mercedes-benz/ardep/_images/heartbeat_led_pcb.png

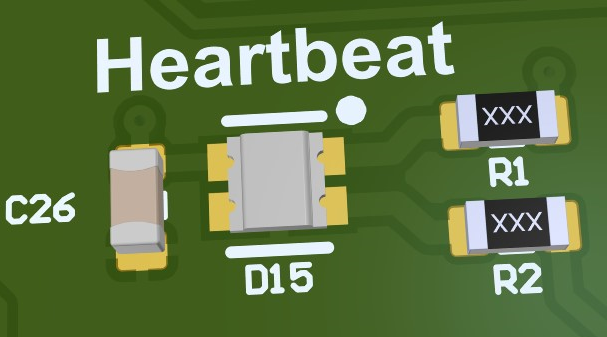
_images/heartbeat_led_pcb.png
