mercedes-benz/ardep/_images/3d_view.png

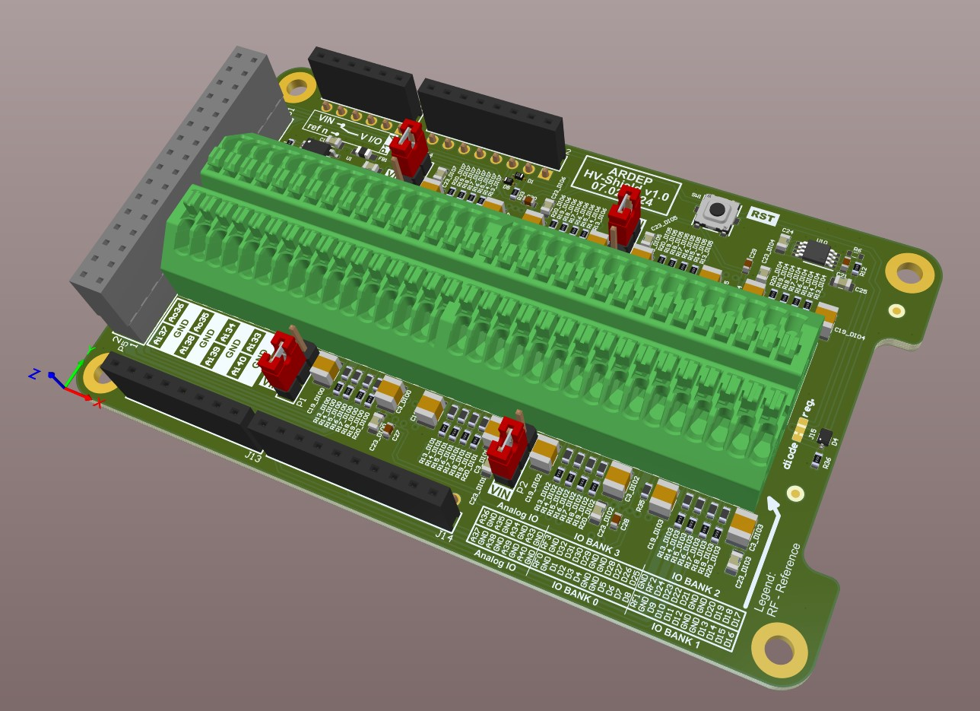
_images/3d_view.png
