mercedes-benz/ardep/_images/3d_view_v1_0_0.png

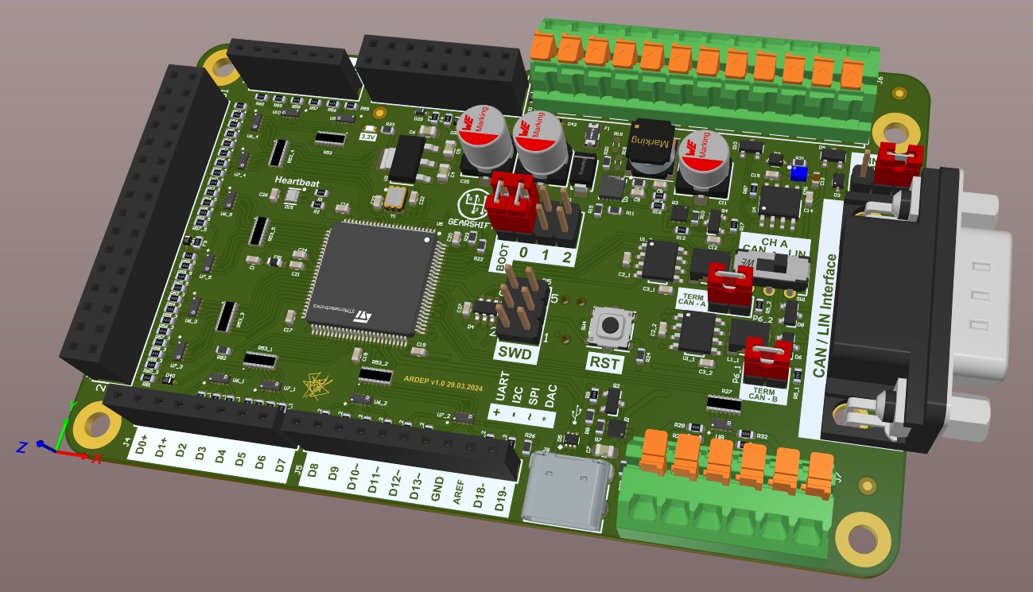
_images/3d_view_v1_0_0.png
