mercedes-benz/ardep/_images/32pin_header_rev0_1.png

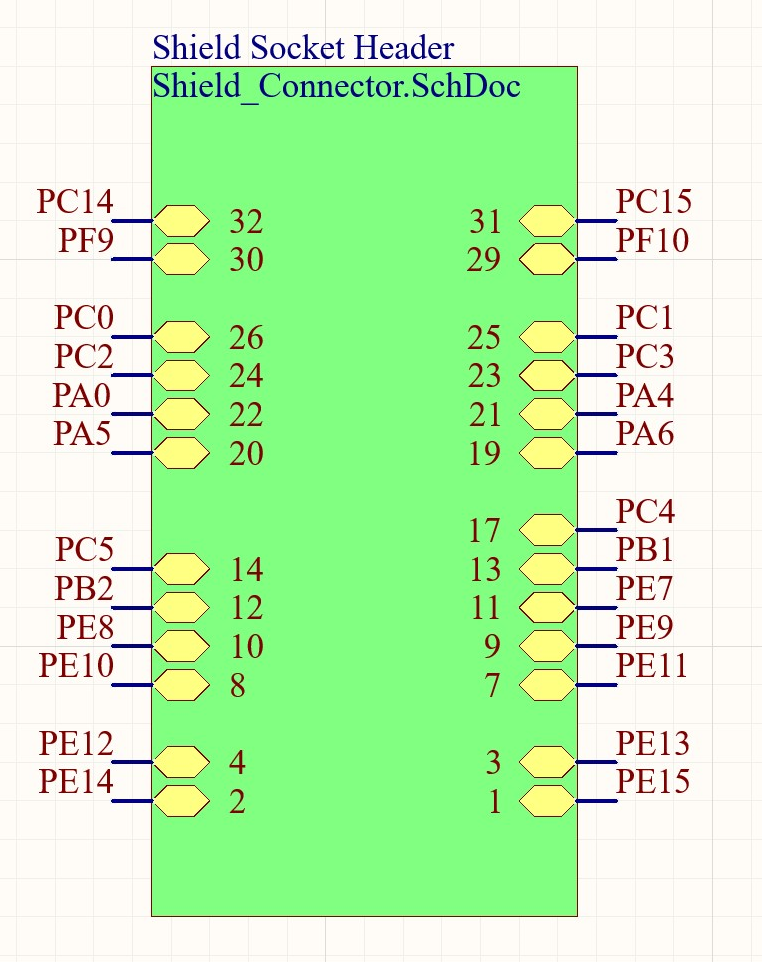
_images/32pin_header_rev0_1.png
