mercedes-benz/ardep/_images/32pin_header_rev0_2.png

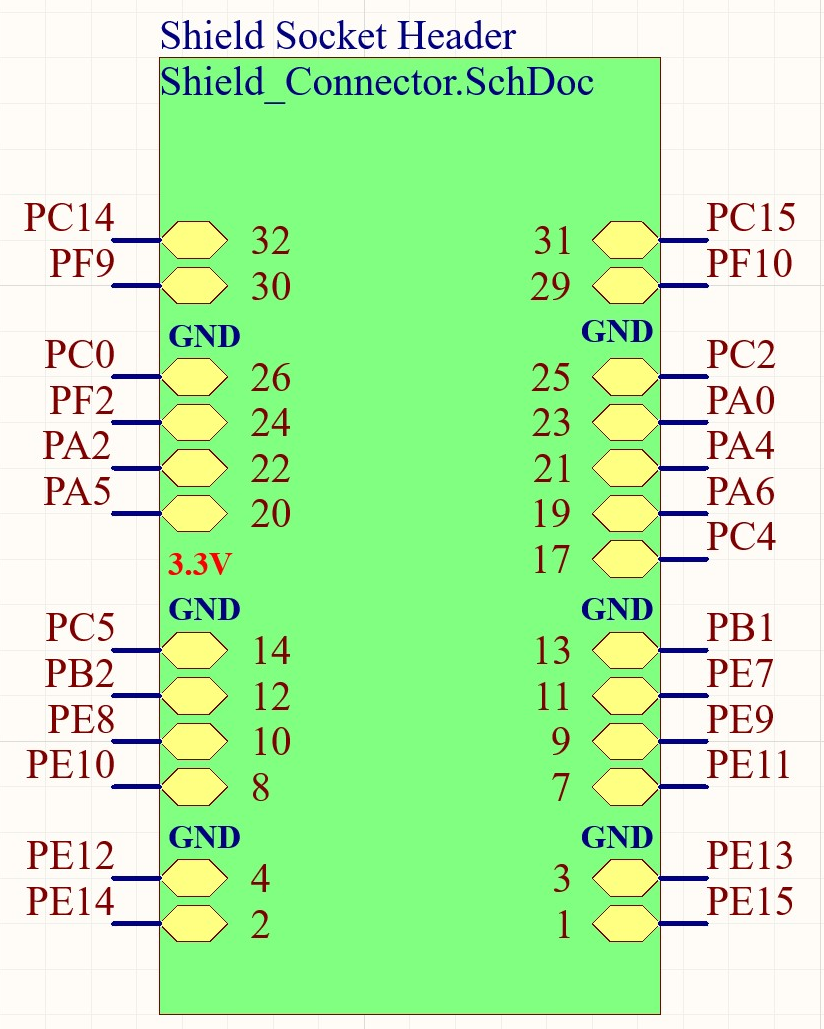
_images/32pin_header_rev0_2.png
