mercedes-benz/ardep/_images/74hc595_implementation.png

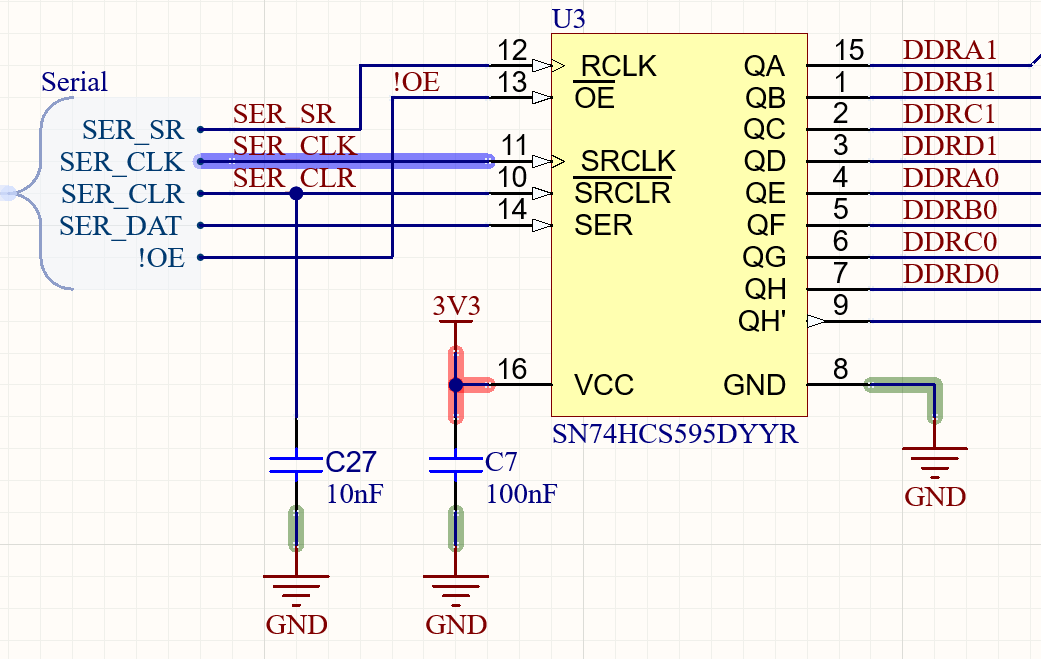
_images/74hc595_implementation.png
