mercedes-benz/ardep/_images/active_input_circuit.png

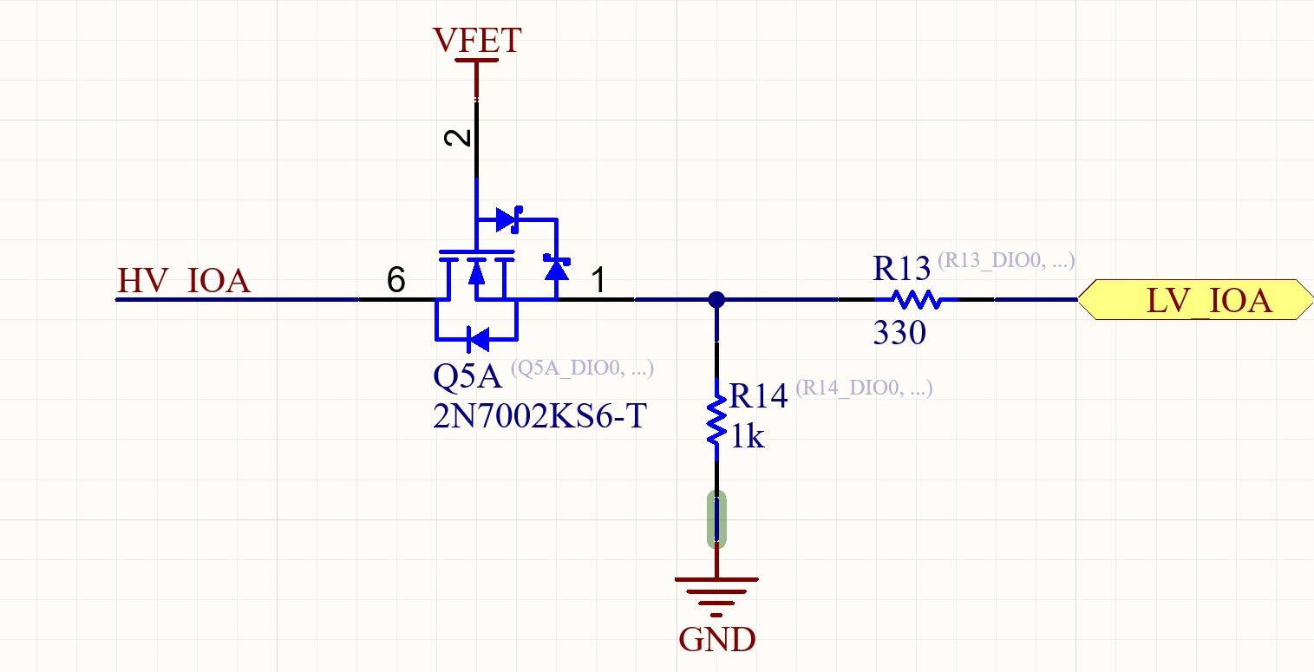
_images/active_input_circuit.png
