mercedes-benz/ardep/_images/analog_gain_amplifier.png

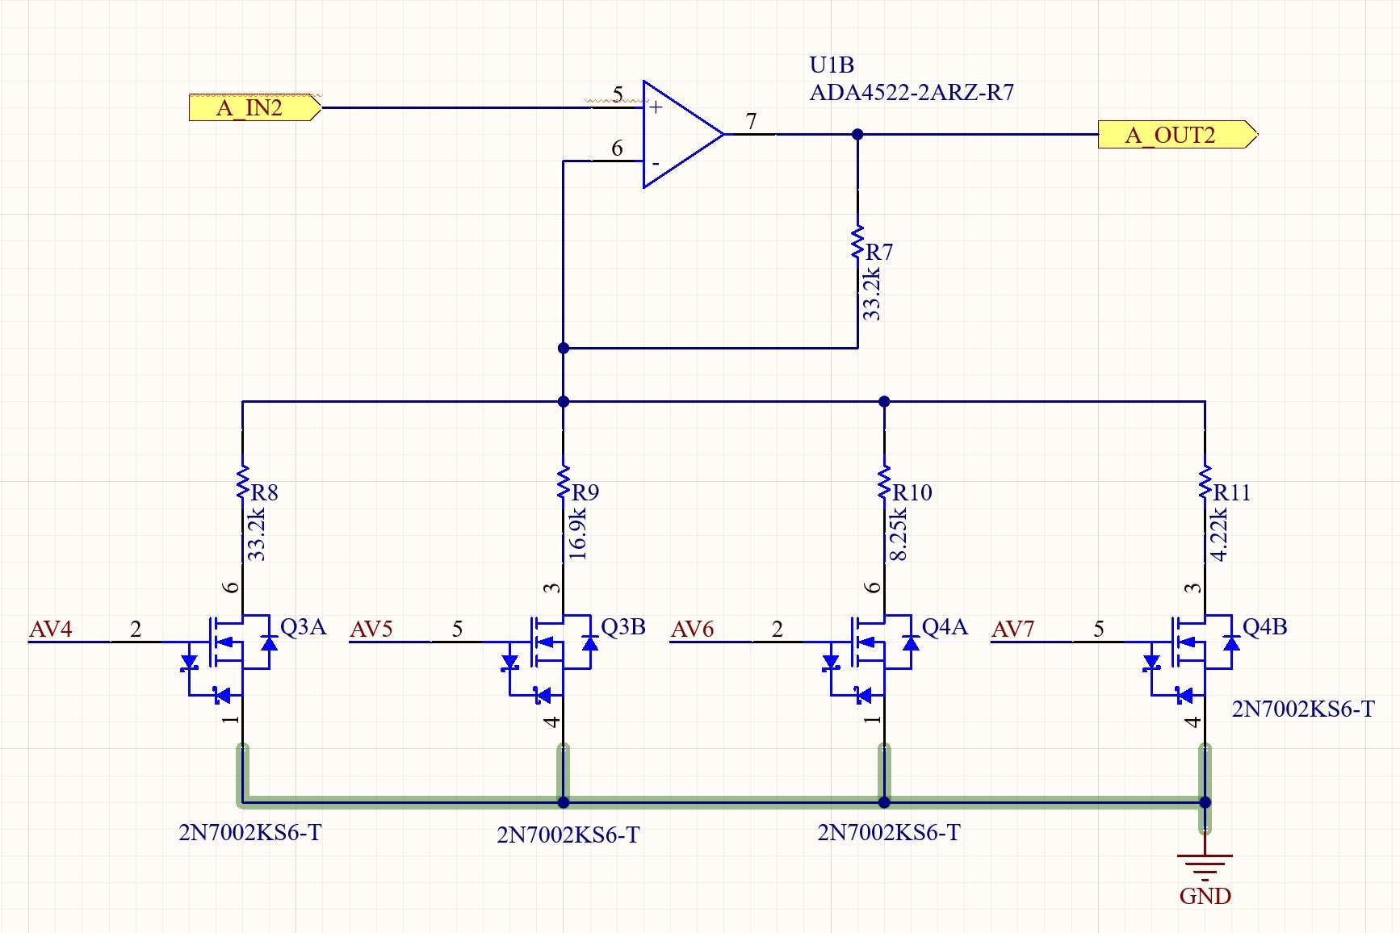
_images/analog_gain_amplifier.png
