mercedes-benz/ardep/_images/can_and_lin_db9_pinout.png

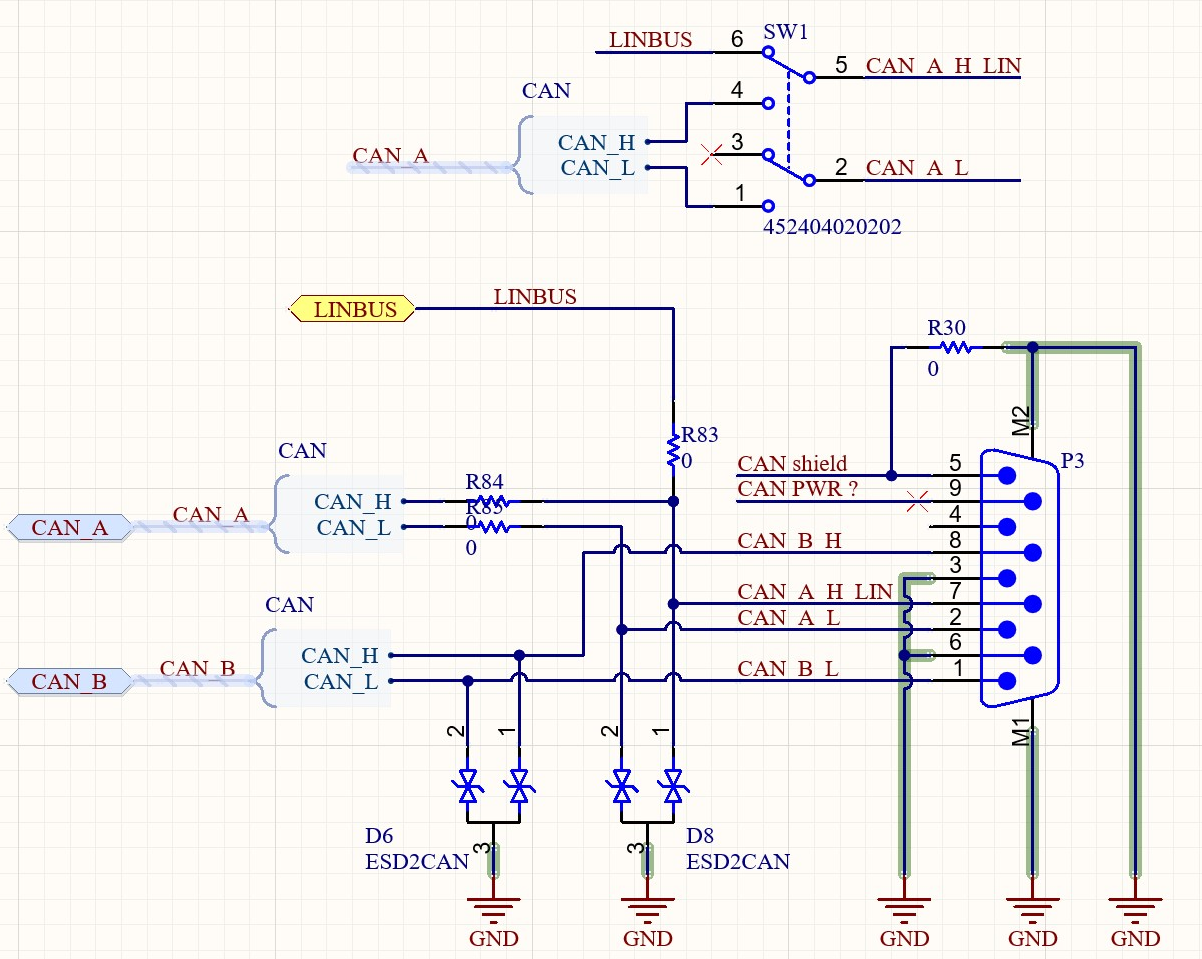
_images/can_and_lin_db9_pinout.png
