mercedes-benz/ardep/_images/can_and_lin_vectors.png

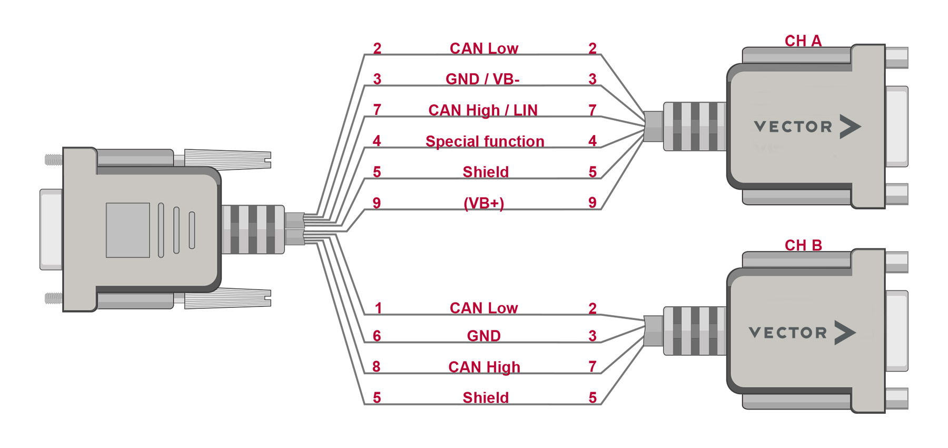
_images/can_and_lin_vectors.png
