mercedes-benz/ardep/_images/can_interface_rev0_1.png

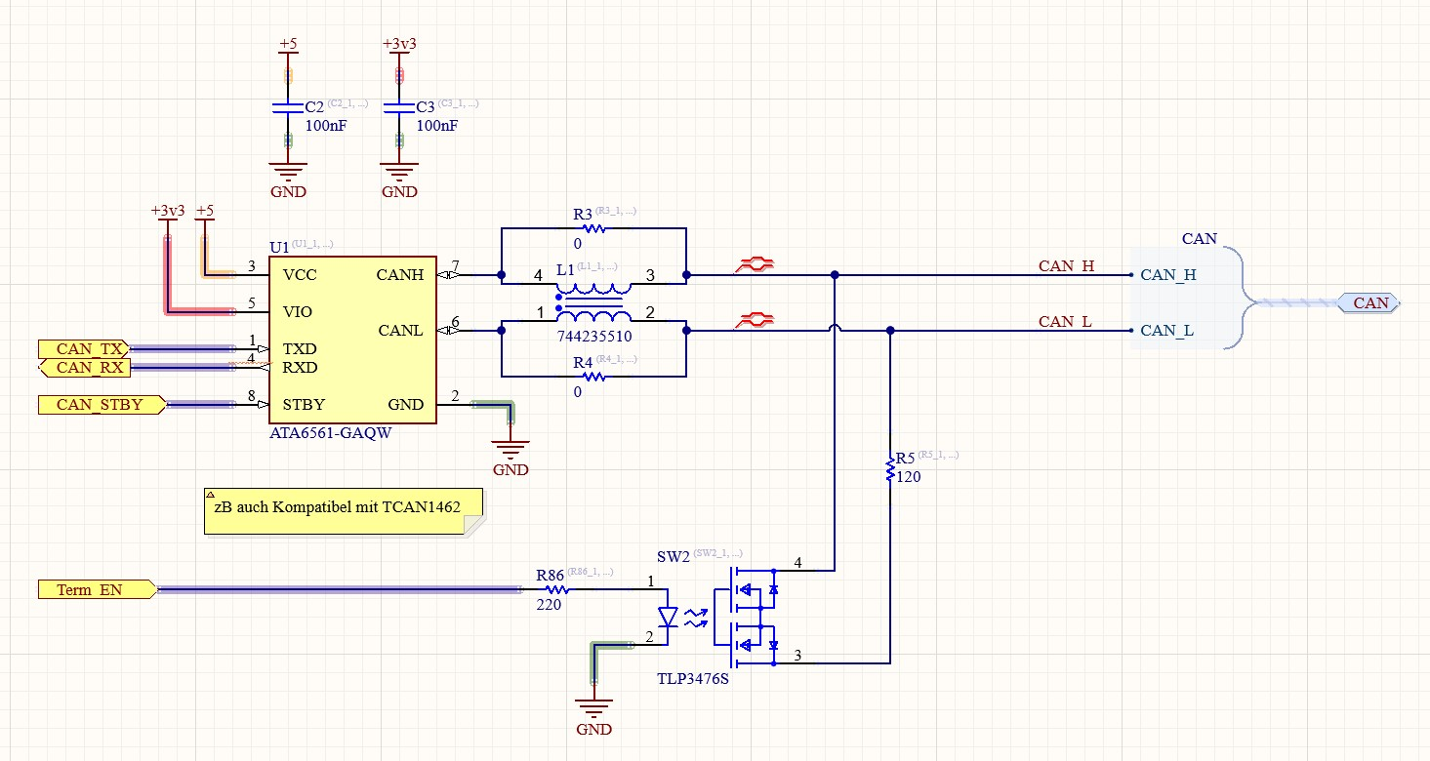
_images/can_interface_rev0_1.png
