mercedes-benz/ardep/_images/can_interface_rev0_2.png

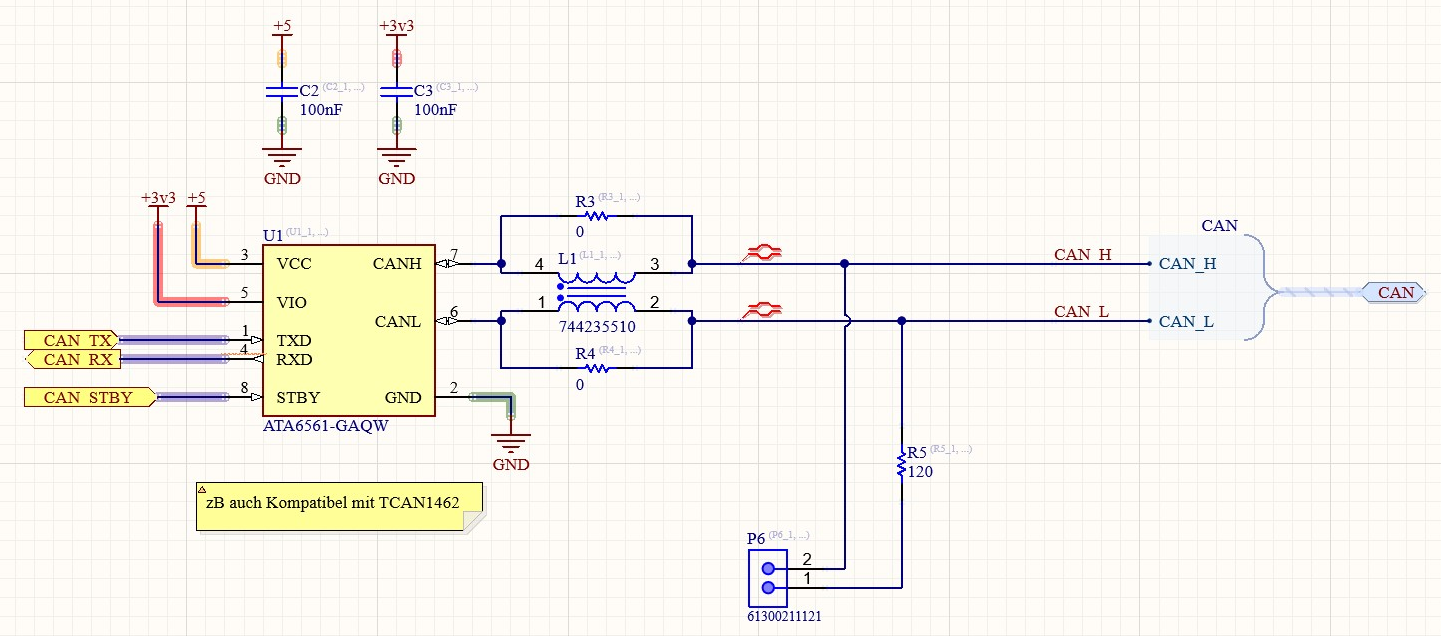
_images/can_interface_rev0_2.png
