mercedes-benz/ardep/_images/digital_io.png

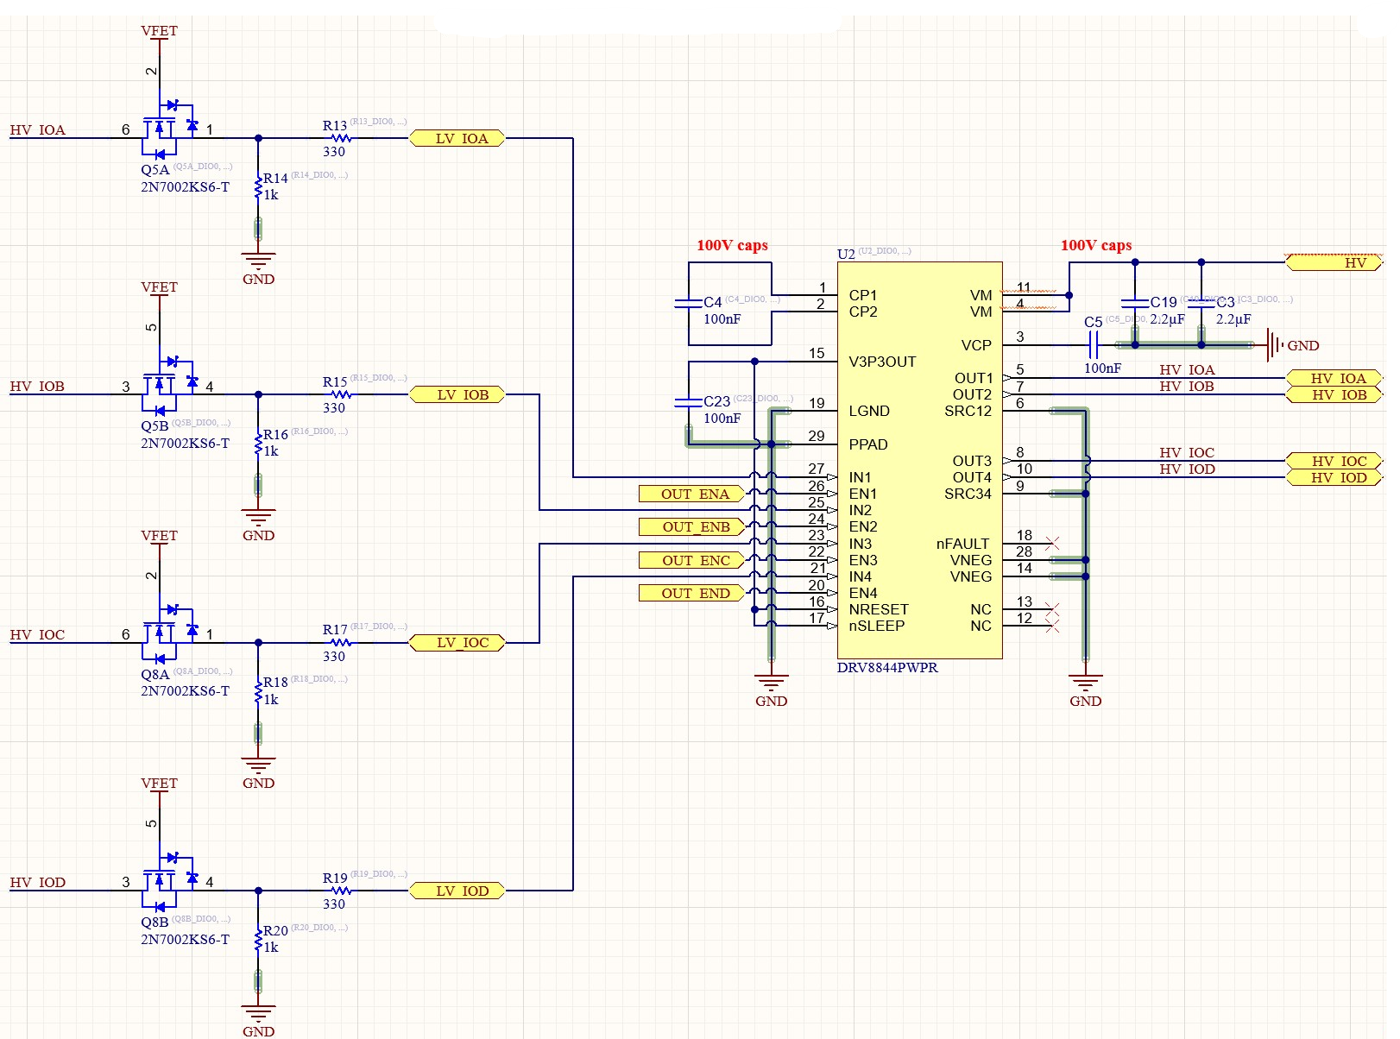
_images/digital_io.png
