mercedes-benz/ardep/_images/gearshift_pcb.png

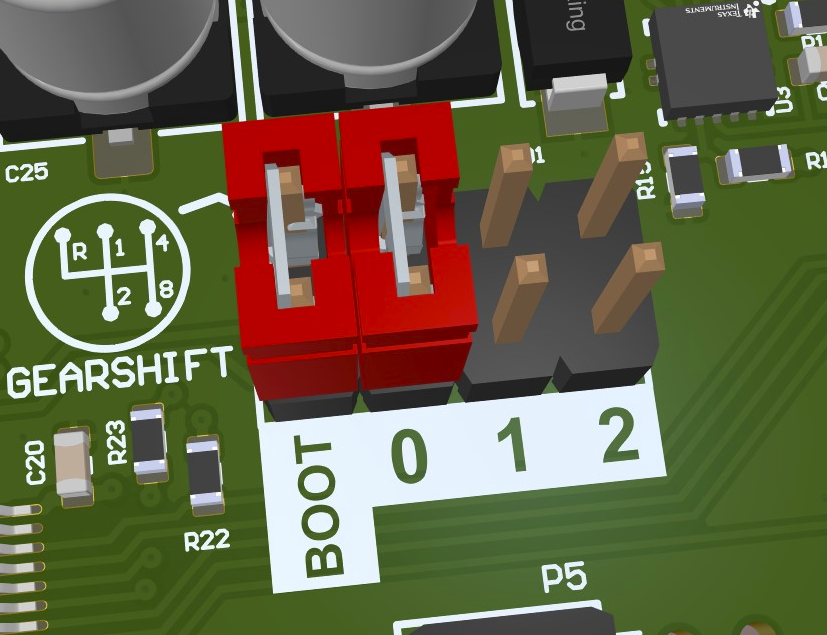
_images/gearshift_pcb.png
