mercedes-benz/ardep/_images/gearshift_schematic.png

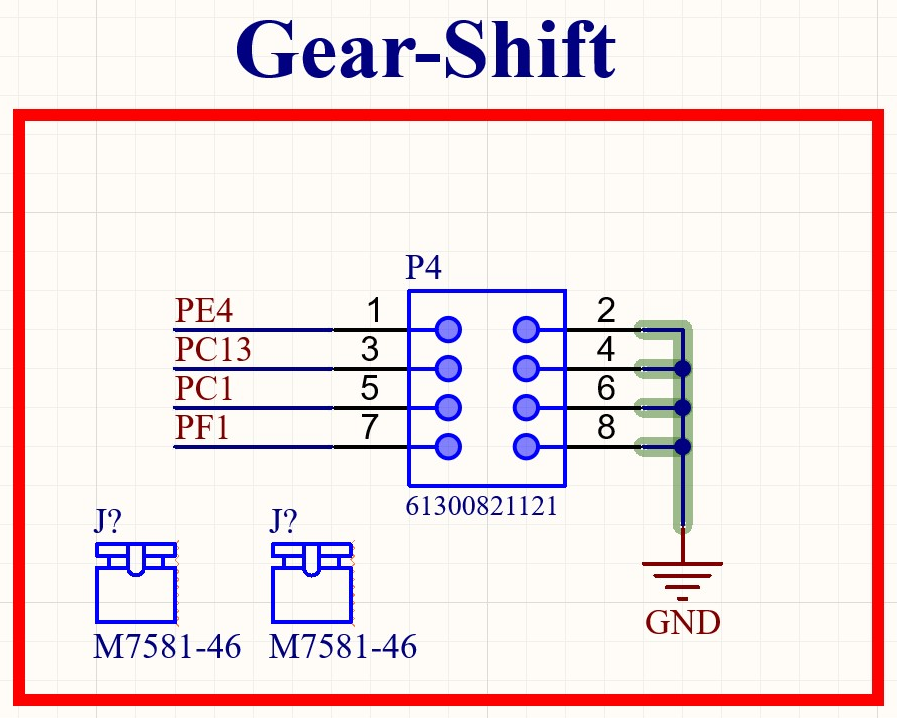
_images/gearshift_schematic.png
