mercedes-benz/ardep/_images/gpio_protective_structure.png

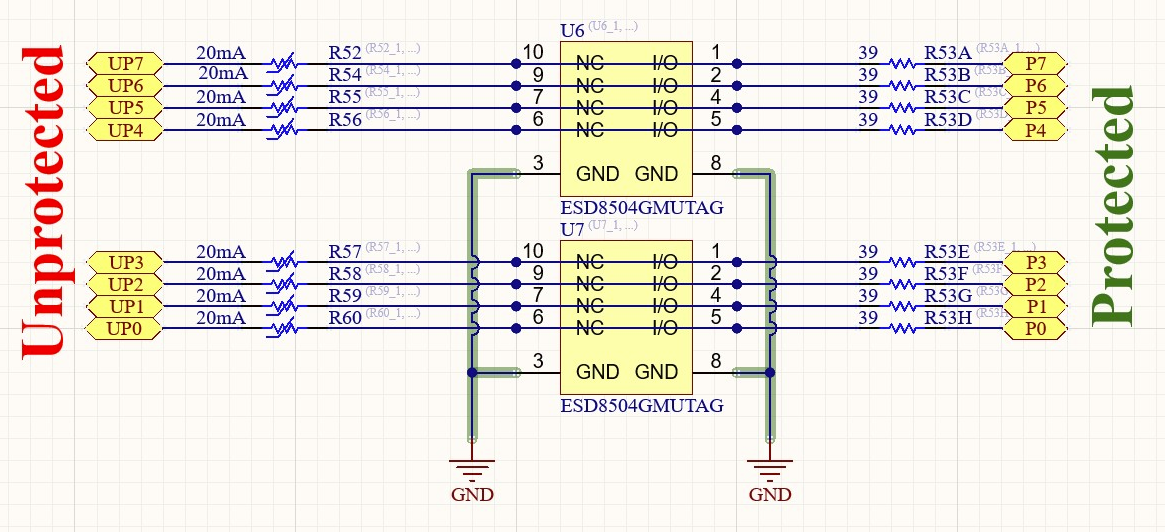
_images/gpio_protective_structure.png
