mercedes-benz/ardep/_images/hv_shield_mosfet_bias_section_voltage_jumper.png

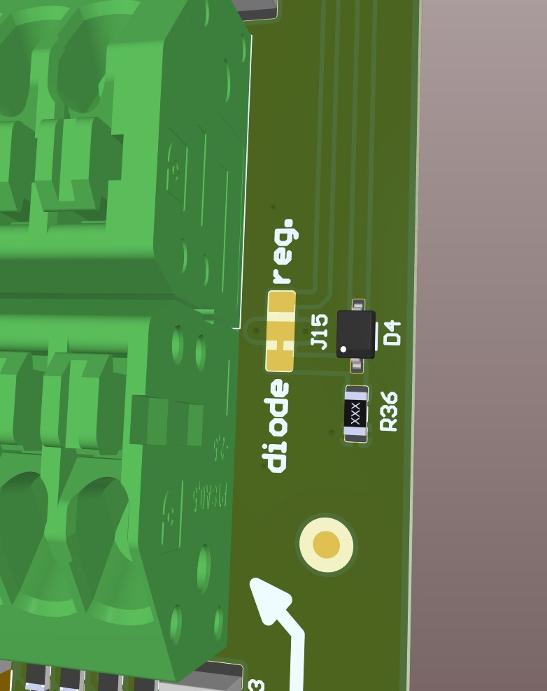
_images/hv_shield_mosfet_bias_section_voltage_jumper.png
