mercedes-benz/ardep/_images/hv_shield_mosfet_bias_voltage_circuit.png

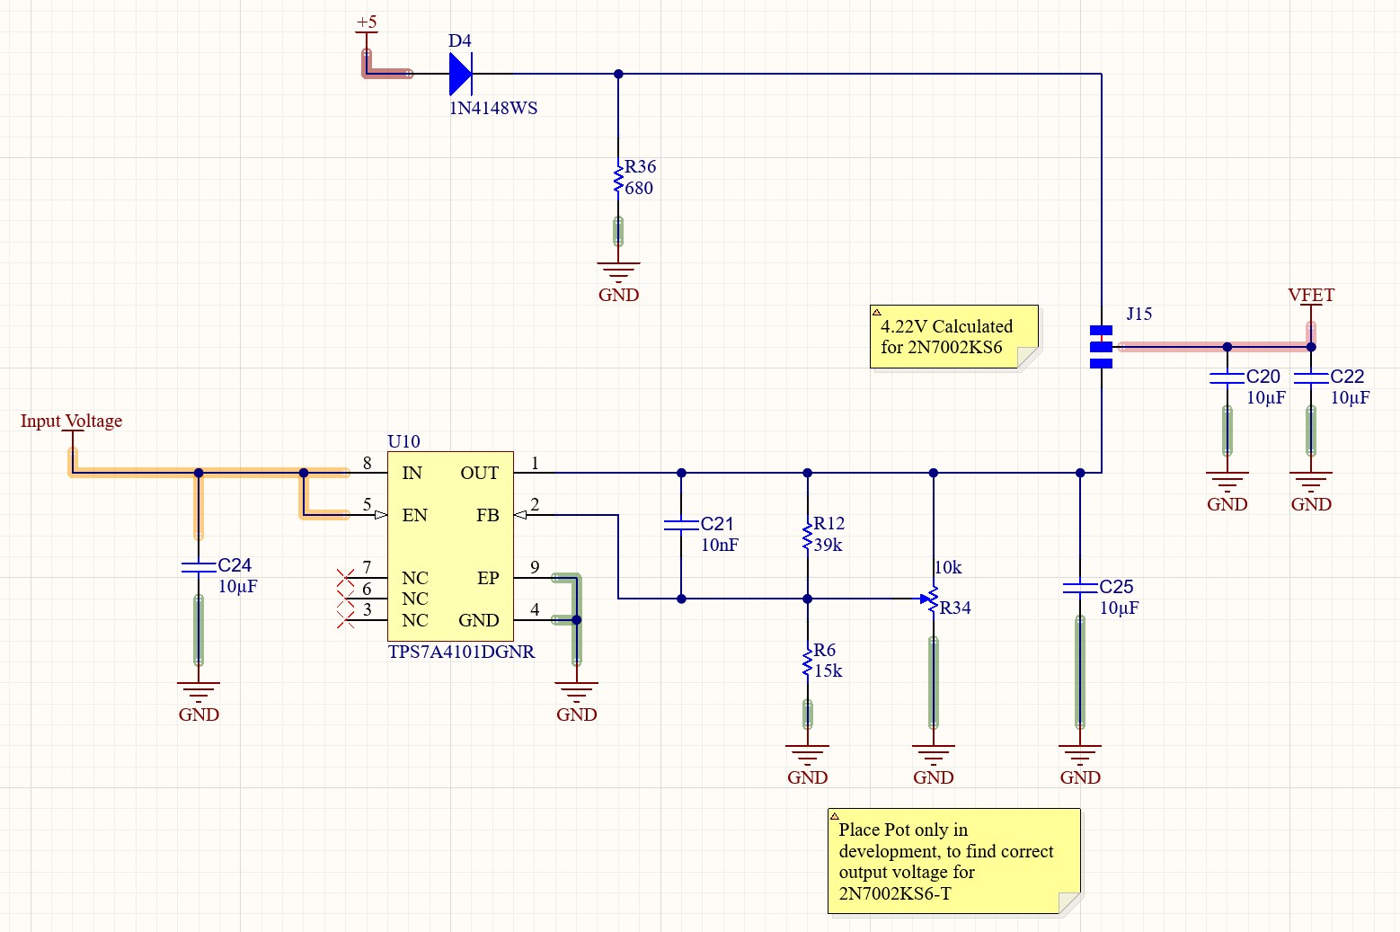
_images/hv_shield_mosfet_bias_voltage_circuit.png
