mercedes-benz/ardep/_images/hv_shield_mosfet_linear_regulator.png

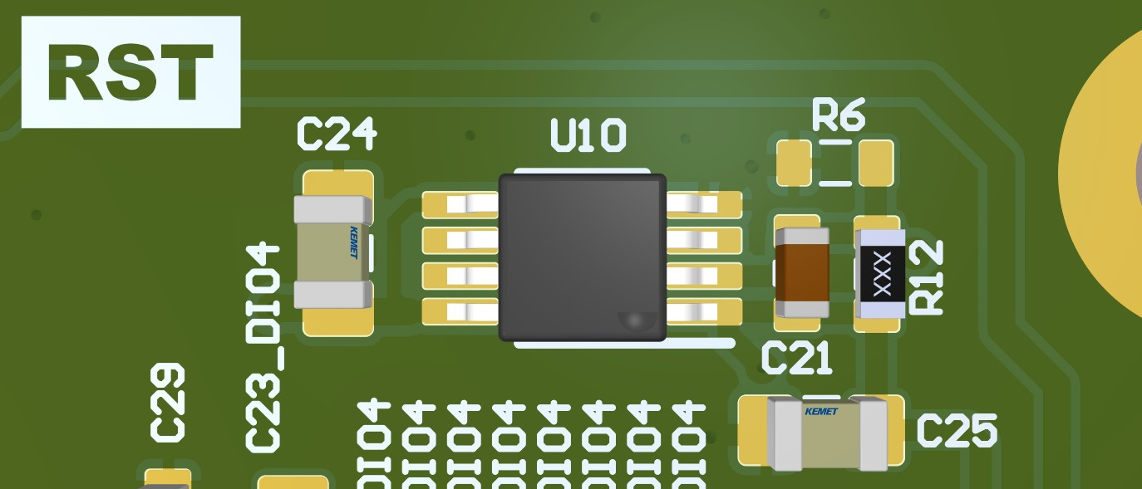
_images/hv_shield_mosfet_linear_regulator.png
