mercedes-benz/ardep/_images/lin_interface.png

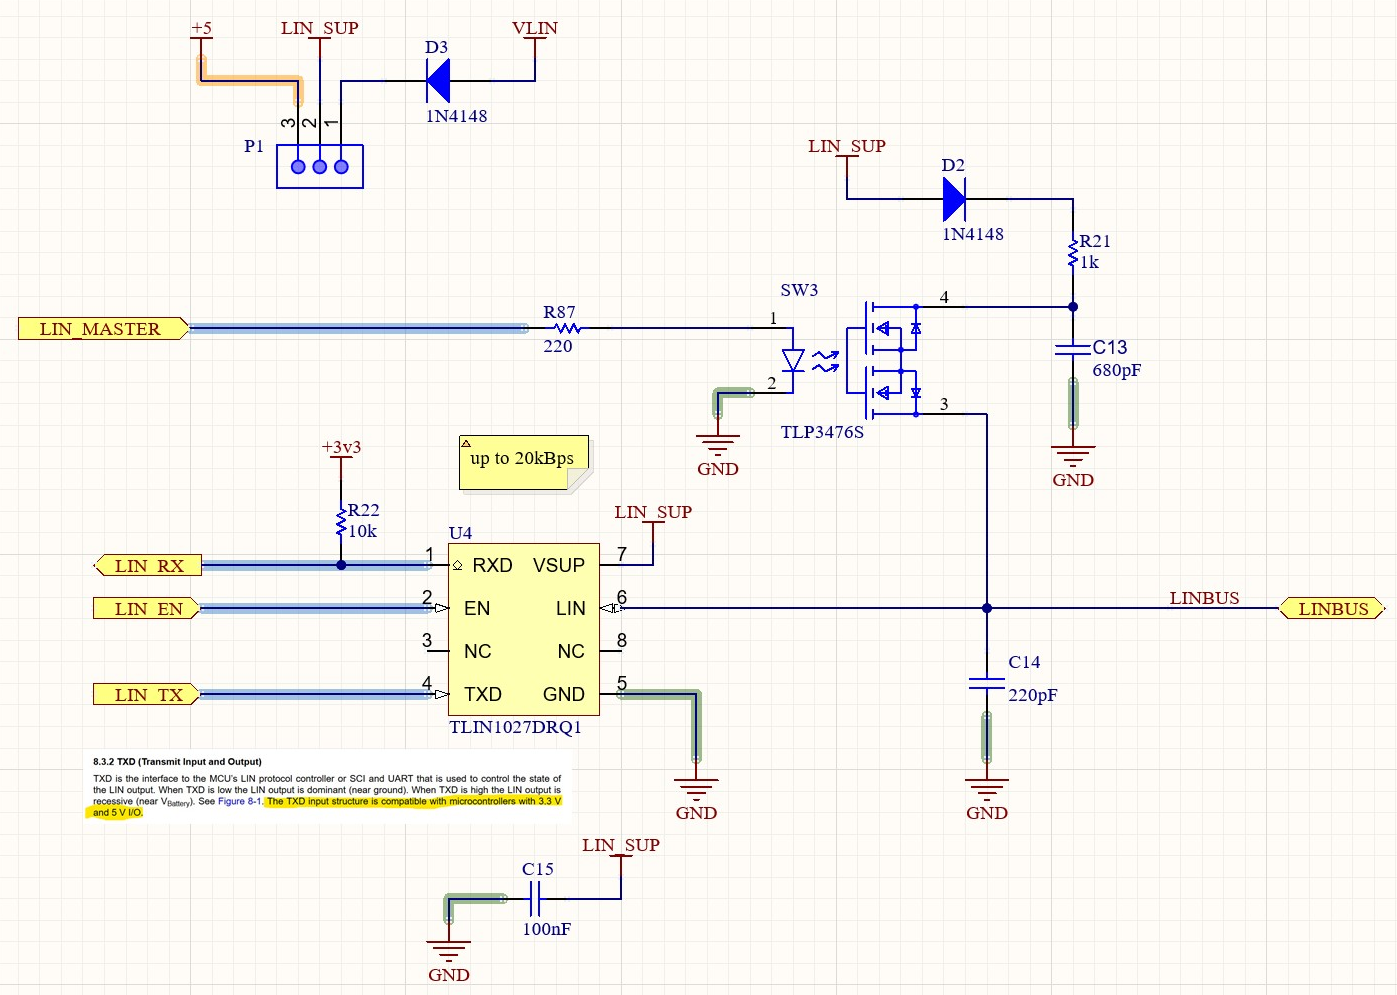
_images/lin_interface.png
