mercedes-benz/ardep/_images/lin_sup_jumper.png

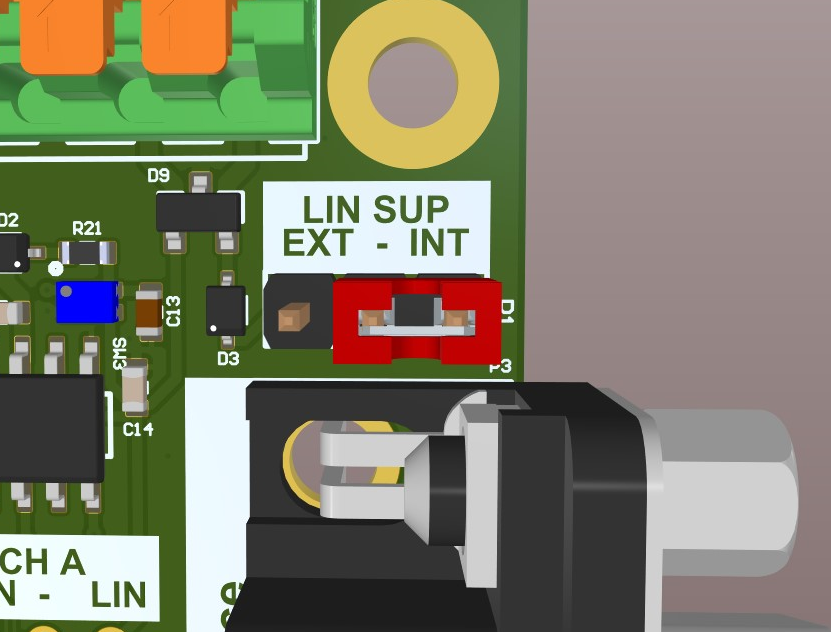
_images/lin_sup_jumper.png
