mercedes-benz/ardep/_images/output_driver.png

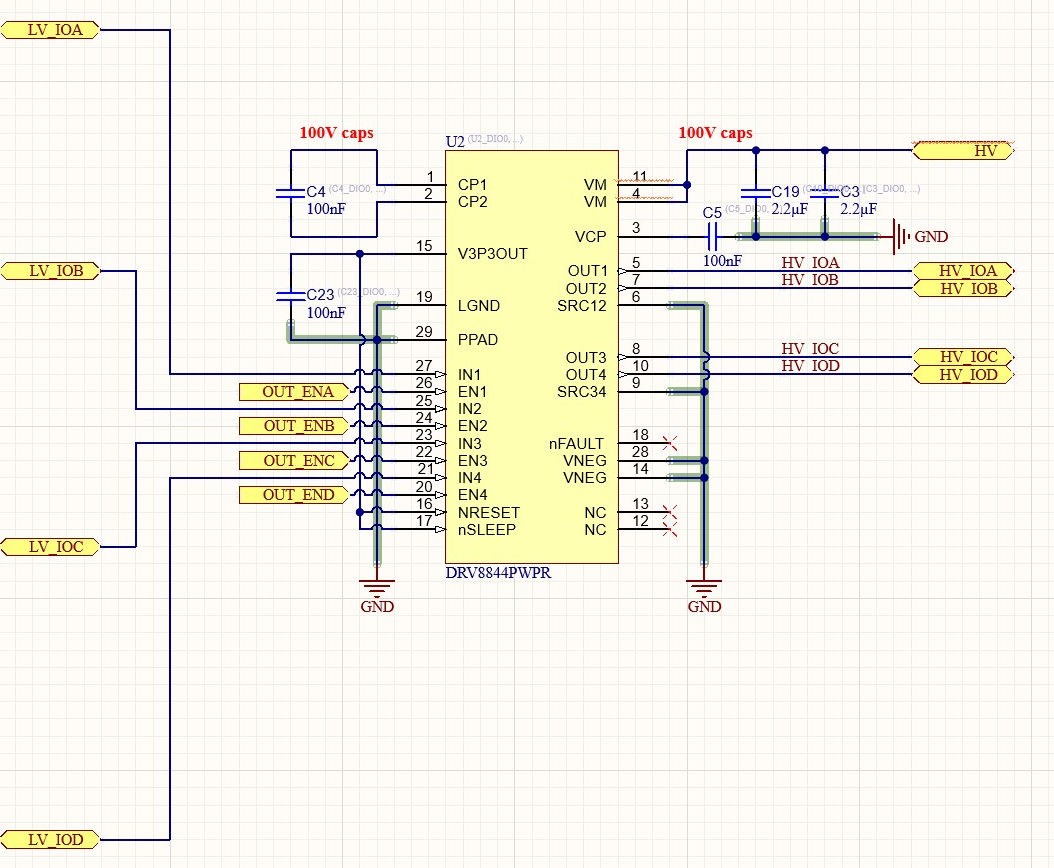
_images/output_driver.png
