mercedes-benz/ardep/_images/output_pin_to_pin_clearance.png

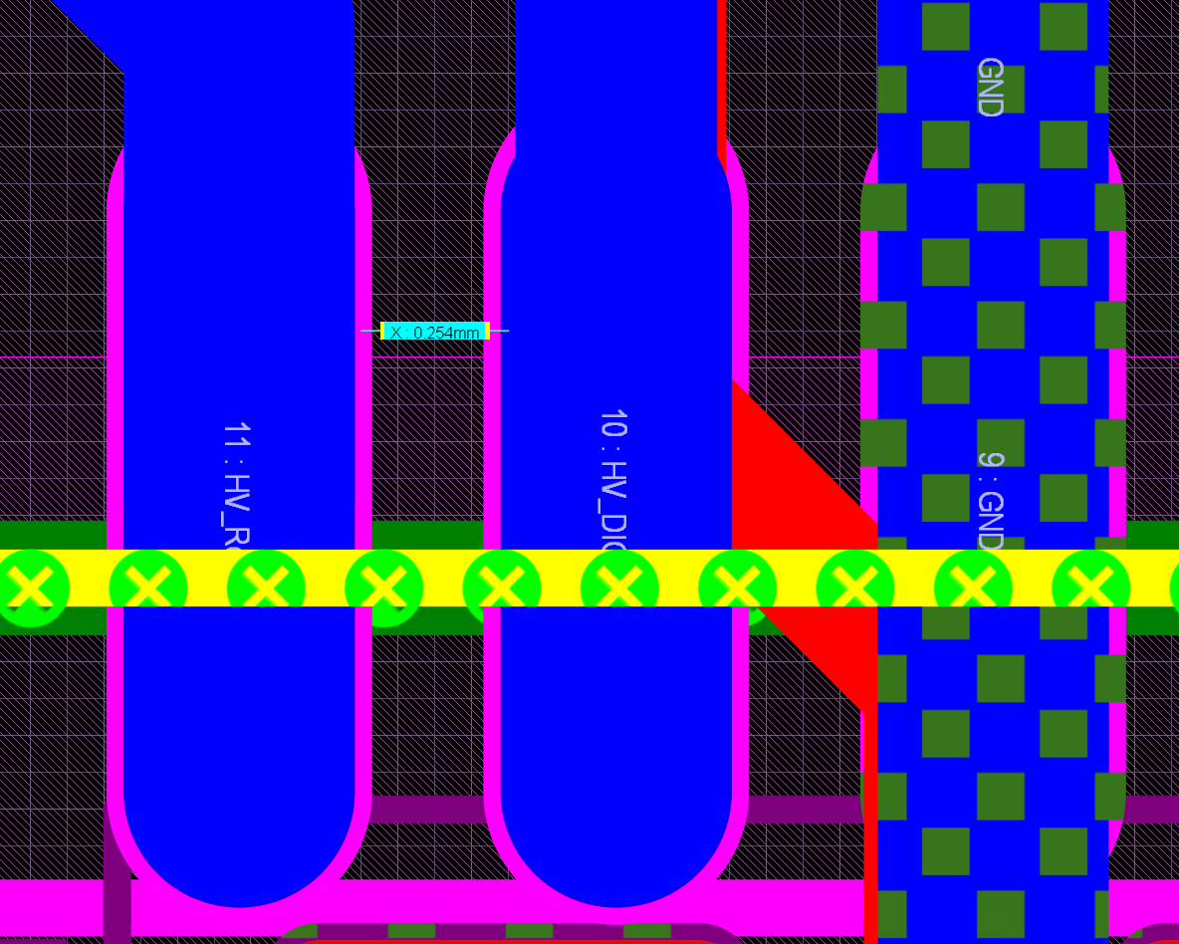
_images/output_pin_to_pin_clearance.png
