mercedes-benz/ardep/_images/pinout1.png

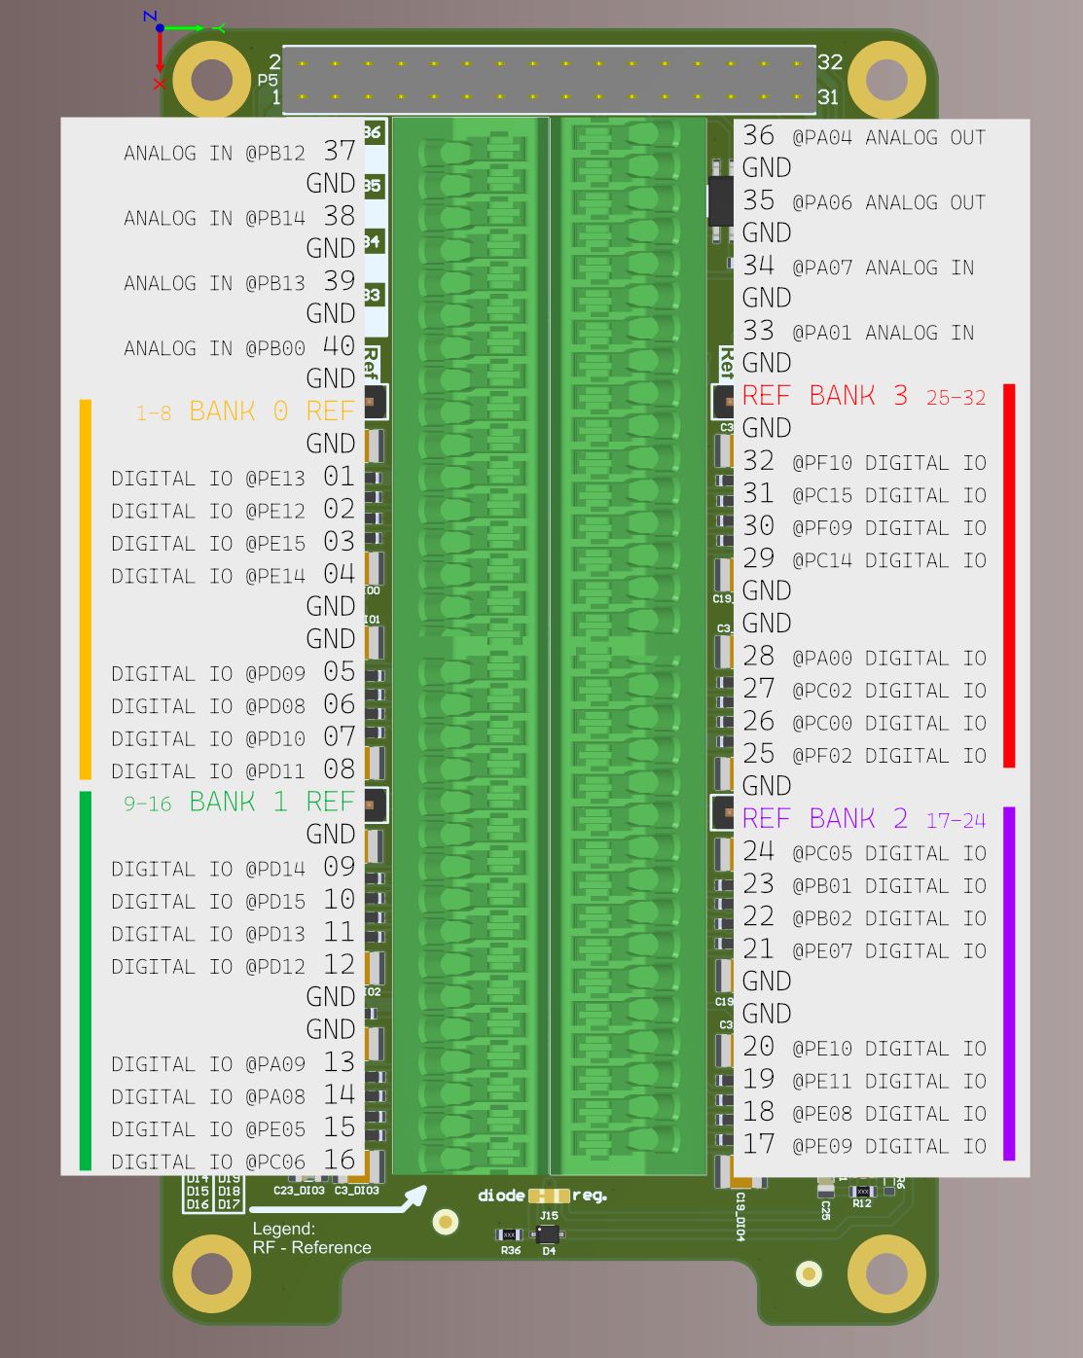
_images/pinout1.png
