mercedes-benz/ardep/_images/rev_0_2.png

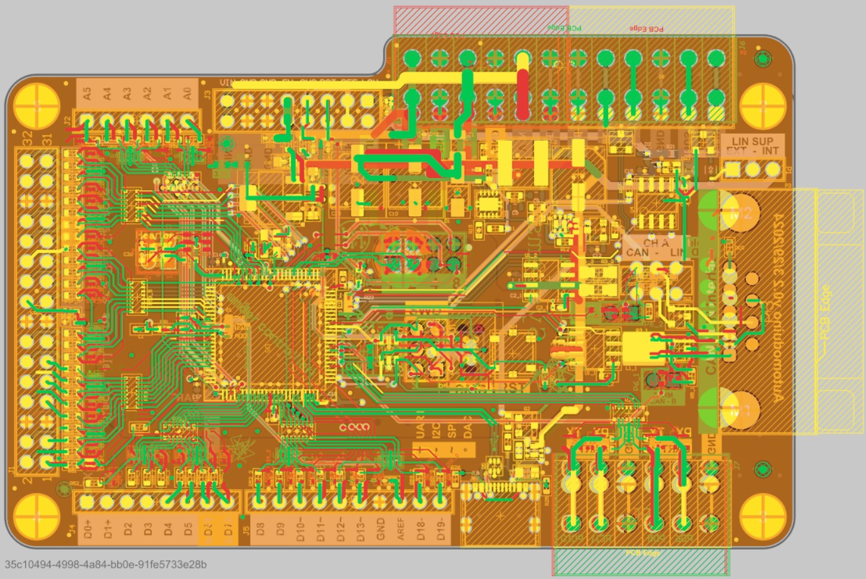
_images/rev_0_2.png
