mercedes-benz/ardep/_images/rev_1_0.png

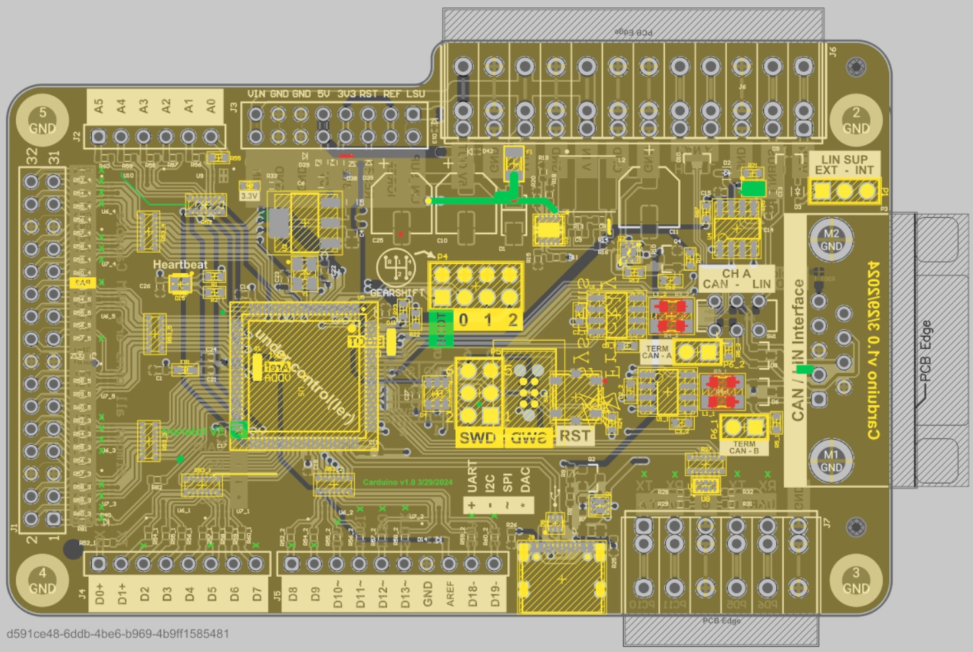
_images/rev_1_0.png
