mercedes-benz/ardep/_images/swd_pinout.png

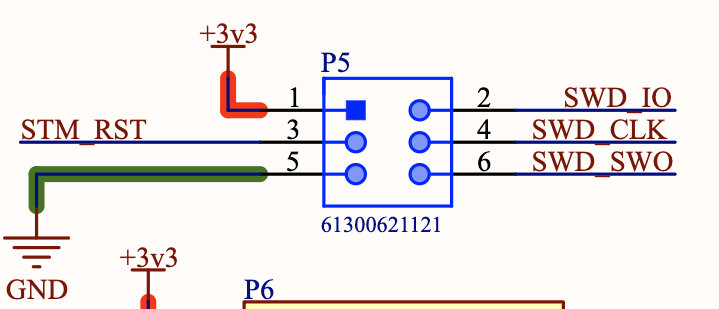
_images/swd_pinout.png
