mercedes-benz/ardep/_images/voltage_divider.png

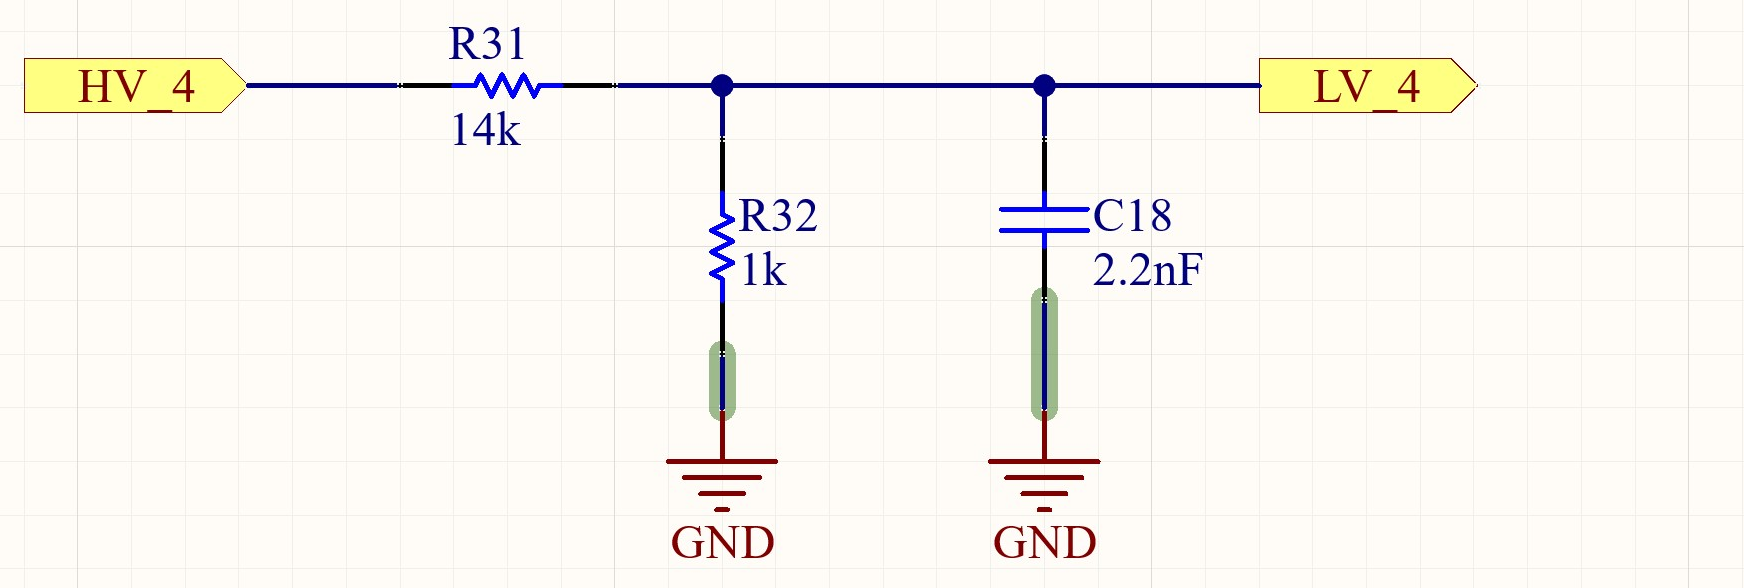
_images/voltage_divider.png
