mercedes-benz/ardep/_images/worst_case_error_margins_1.png

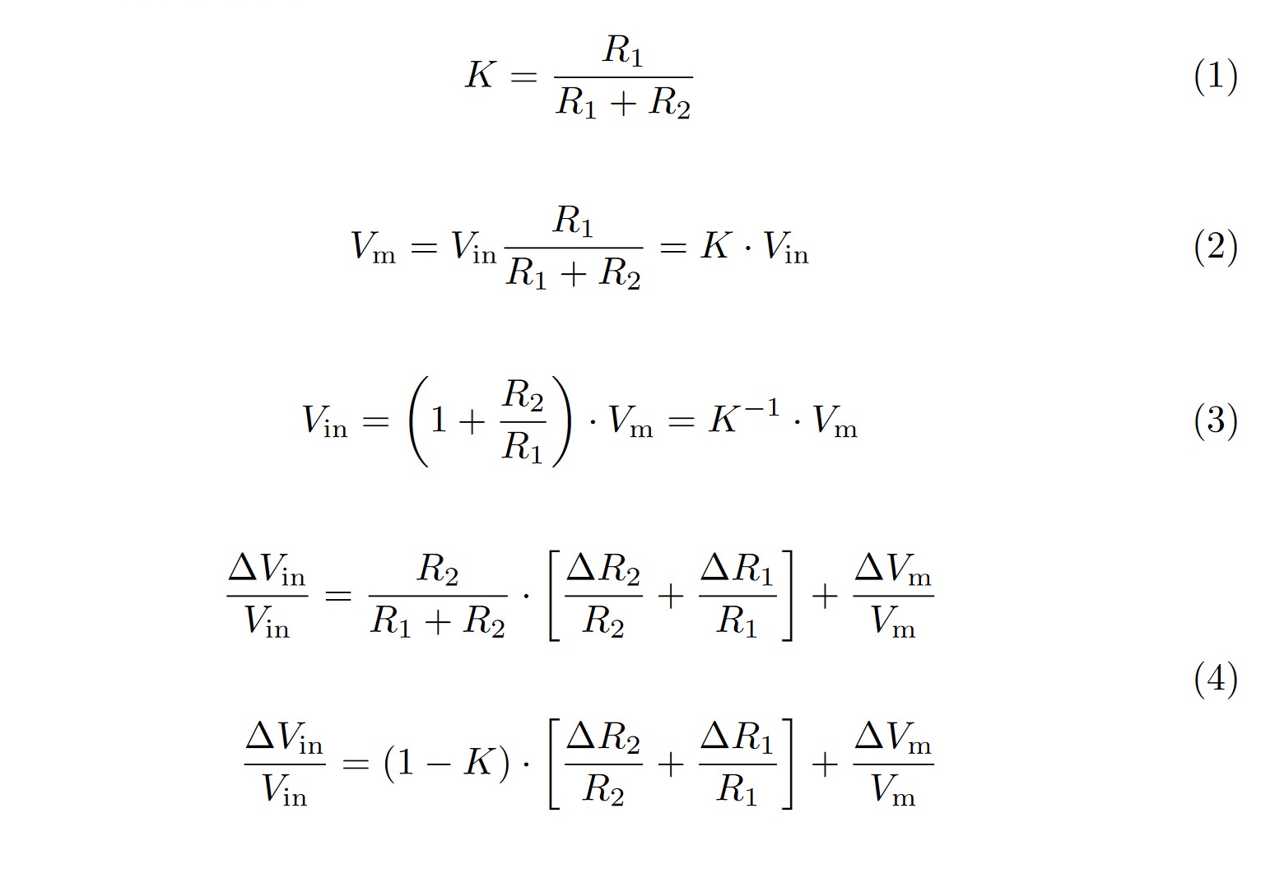
_images/worst_case_error_margins_1.png
