mercedes-benz/ardep/_images/worst_case_error_margins_2.png

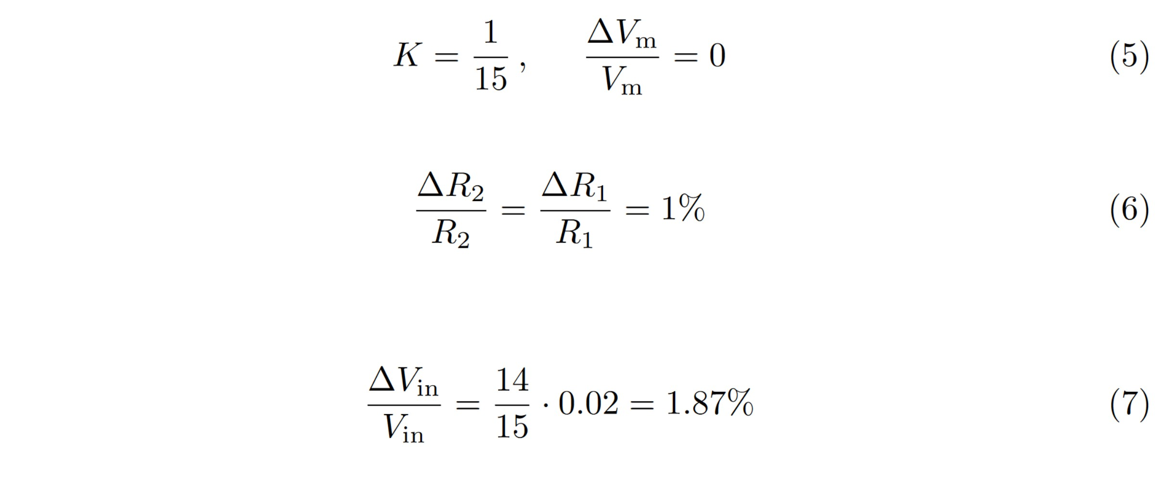
_images/worst_case_error_margins_2.png
