mercedes-benz/ardep/hardware/openSCAD_model/ardep_enclosure.png

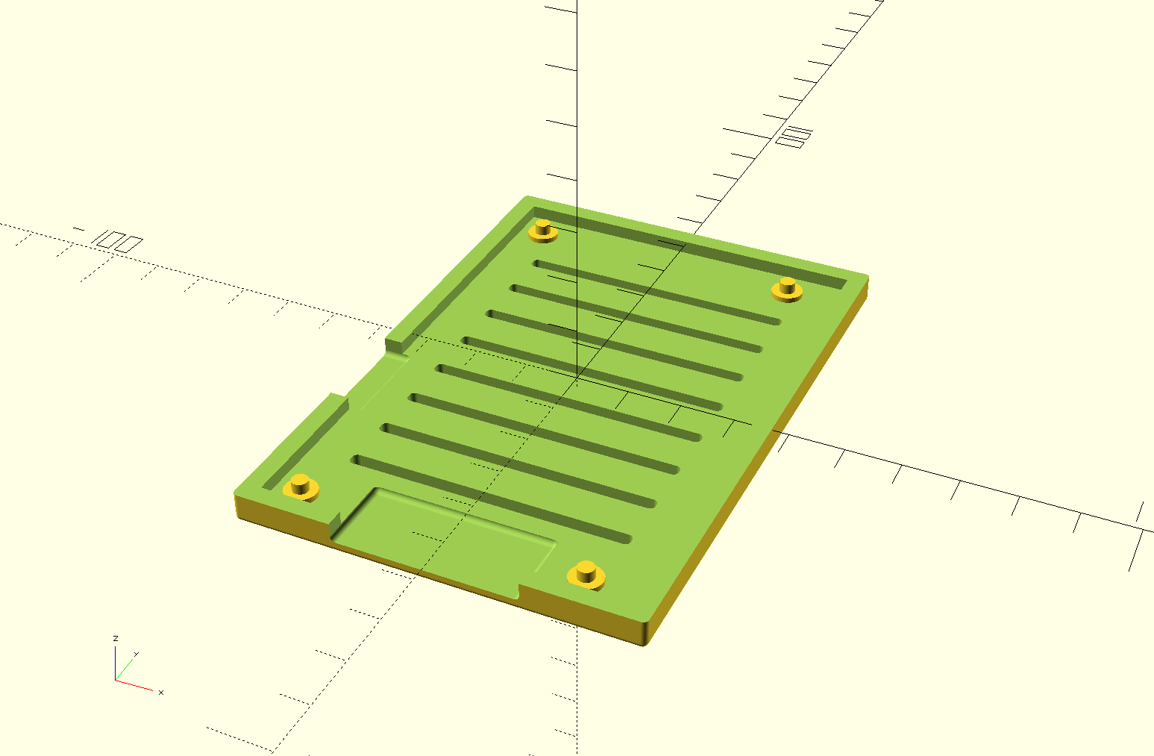
hardware/openSCAD_model/ardep_enclosure.png
