mercedes-benz/ardep/_images/windows_install_usb_driver.png

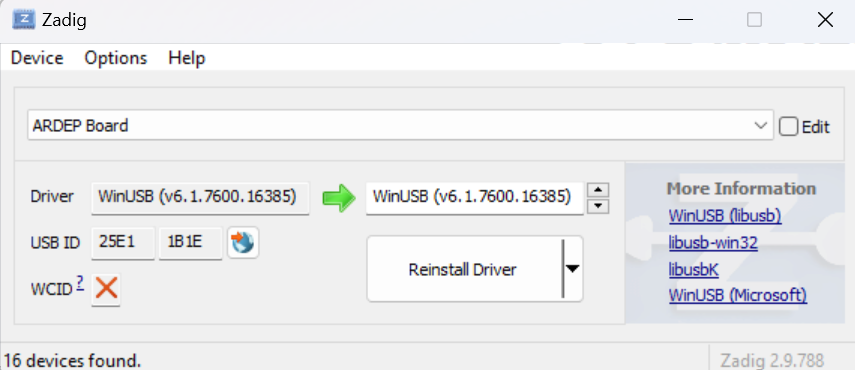
_images/windows_install_usb_driver.png
