mercedes-benz/ardep/_images/measurement.png

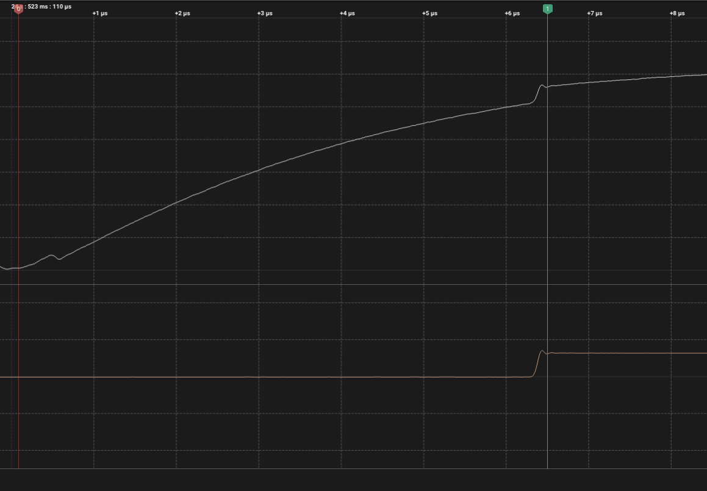
_images/measurement.png
