mercedes-benz/ardep/_images/debugger_schematic_v2_0_0.png

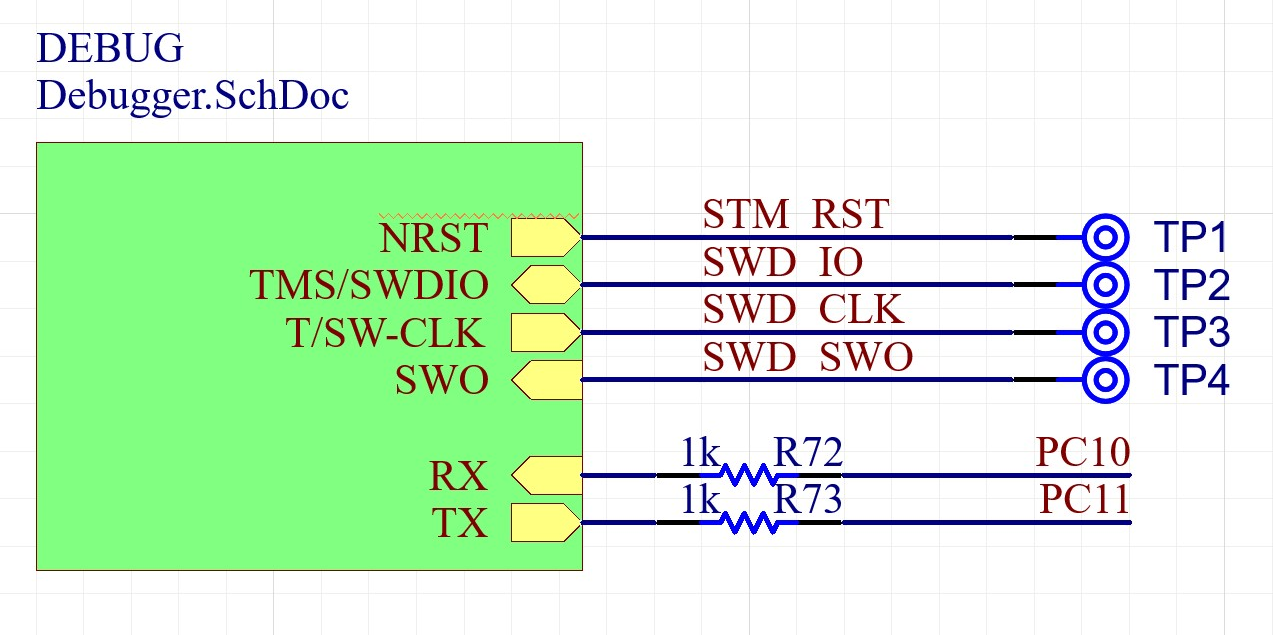
_images/debugger_schematic_v2_0_0.png
